BMHX/modelyard-hardware/assets/images/forge60-product-2.jpg

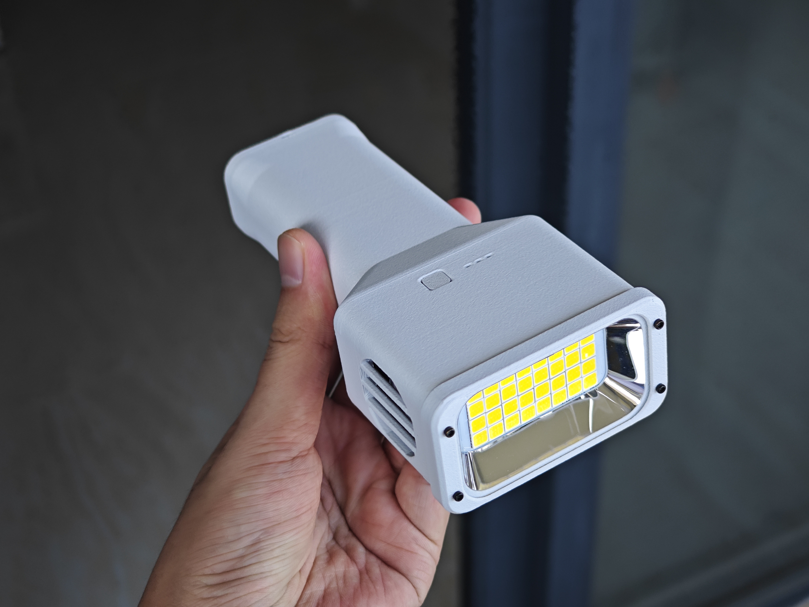
assets/images/forge60-product-2.jpg
