BMHX/modelyard-hardware/assets/images/forge60-product-3.jpg

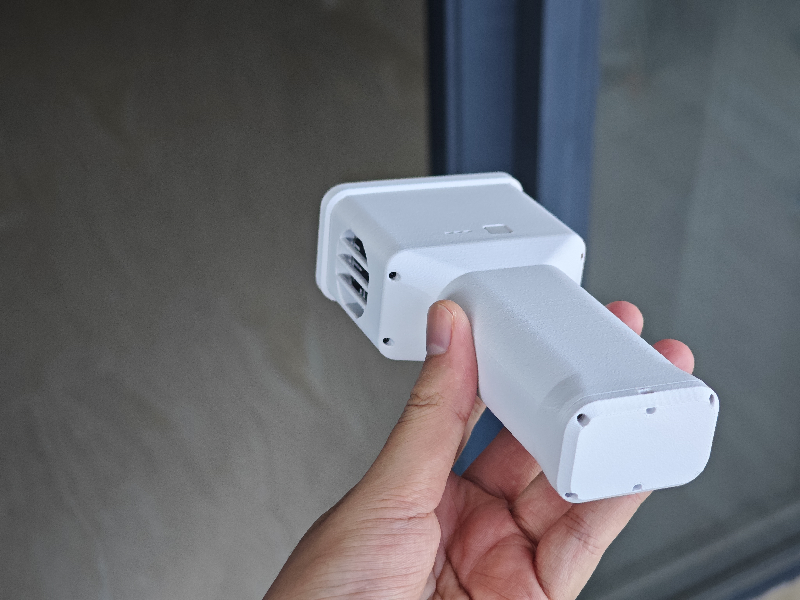
assets/images/forge60-product-3.jpg
