BMHX/modelyard-hardware/Forgeos Firmware/Forgeos v1.2User_Guide (1).jpg

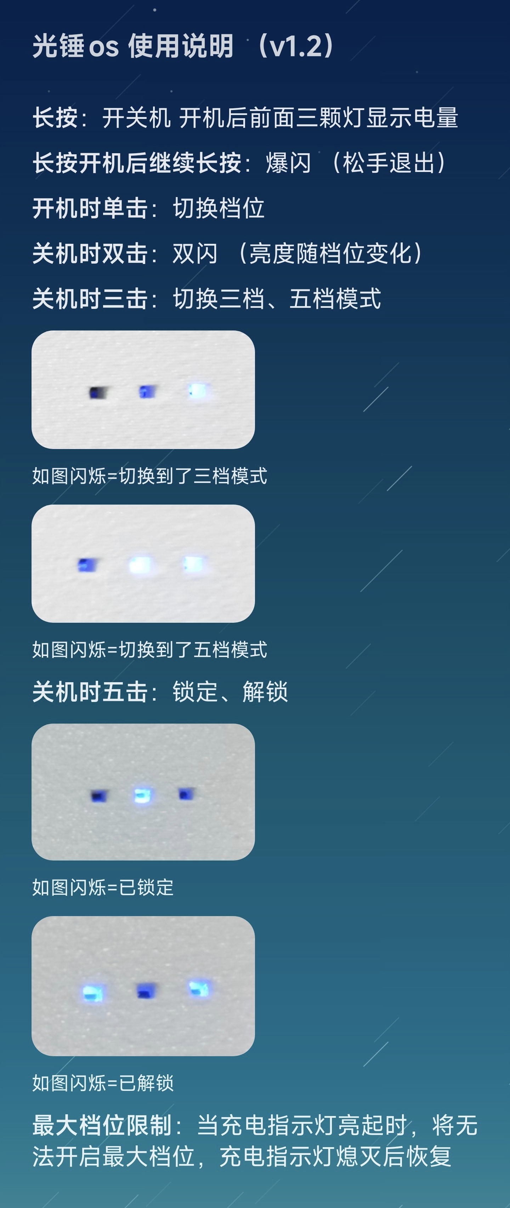
Forgeos Firmware/Forgeos v1.2User_Guide (1).jpg
